mayopan/Tire-warmer-power-board/spice/Tire Warmer.asc

C4: cap; 1µ
C5: cap; 1µ
D1: LED; NSCW100
D3: LED; NSCW100
M2: nmos; IRF3205
M3: nmos; BSS138/FAI
M4: nmos; IRF3205
Q4: npn; ss8050
R1: res; 10k
R3: res; 100
R9: res; 10k
R10: res; 1k
R11: res; 7
R12: res; 1k
R13: res; 7
R14: res; 100
V1: voltage; 12
V2: voltage; 3.3
V3: voltage; PULSE(0 3.3 50u 1u 1u {TON} {T} 10)
Named nets: 0, Vcc2, Vcc1, Pulse, fs, fg, fg2, fs2, tb, tb2
.tran 0 {T*10} 10us
.param D=0.9
.param F=733
.param T=1/F
.param TON=D*T
.inc irf3205.spi
.inc ss8050.lib
.inc ss8550.lib
.inc BSS138.lib
BSS 138 FET version
SS8050 transistor version
